12zcab/Handheld-Z80-Retro-Computer/img/PCB.png

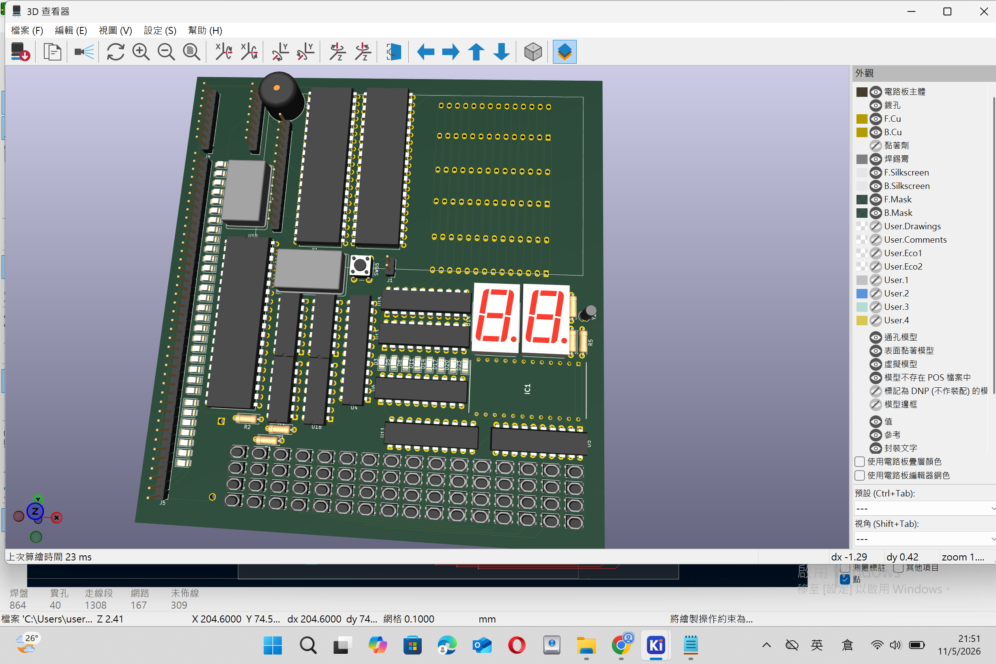
img/PCB.png
