12zcab/Handheld-Z80-Retro-Computer/img/PCBold.png

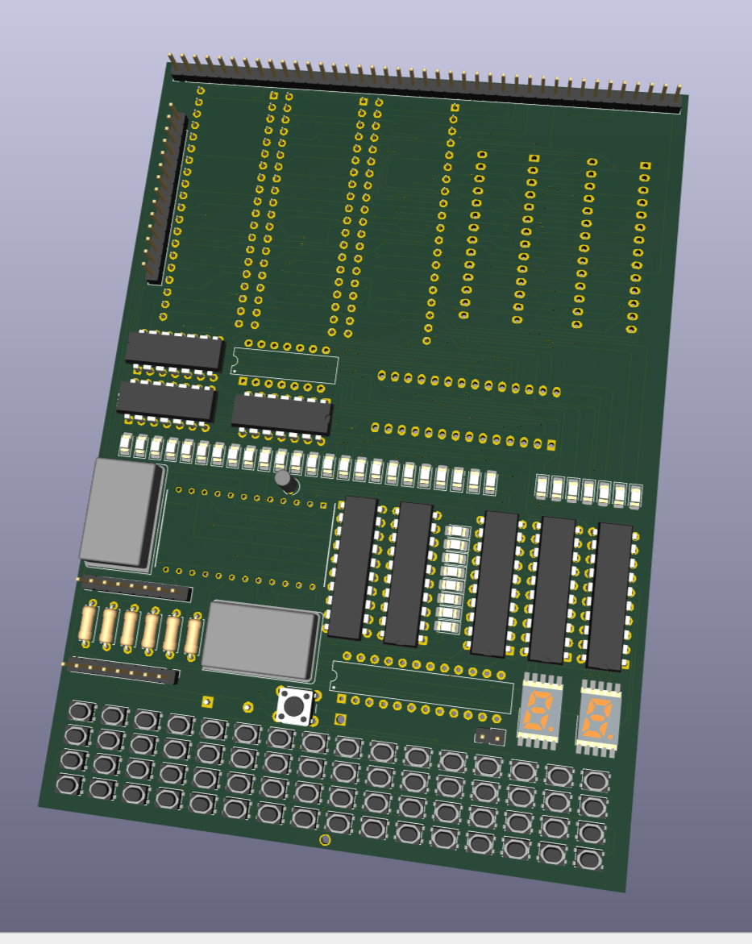
img/PCBold.png
