12zcab/Handheld-Z80-Retro-Computer/img/Route.png

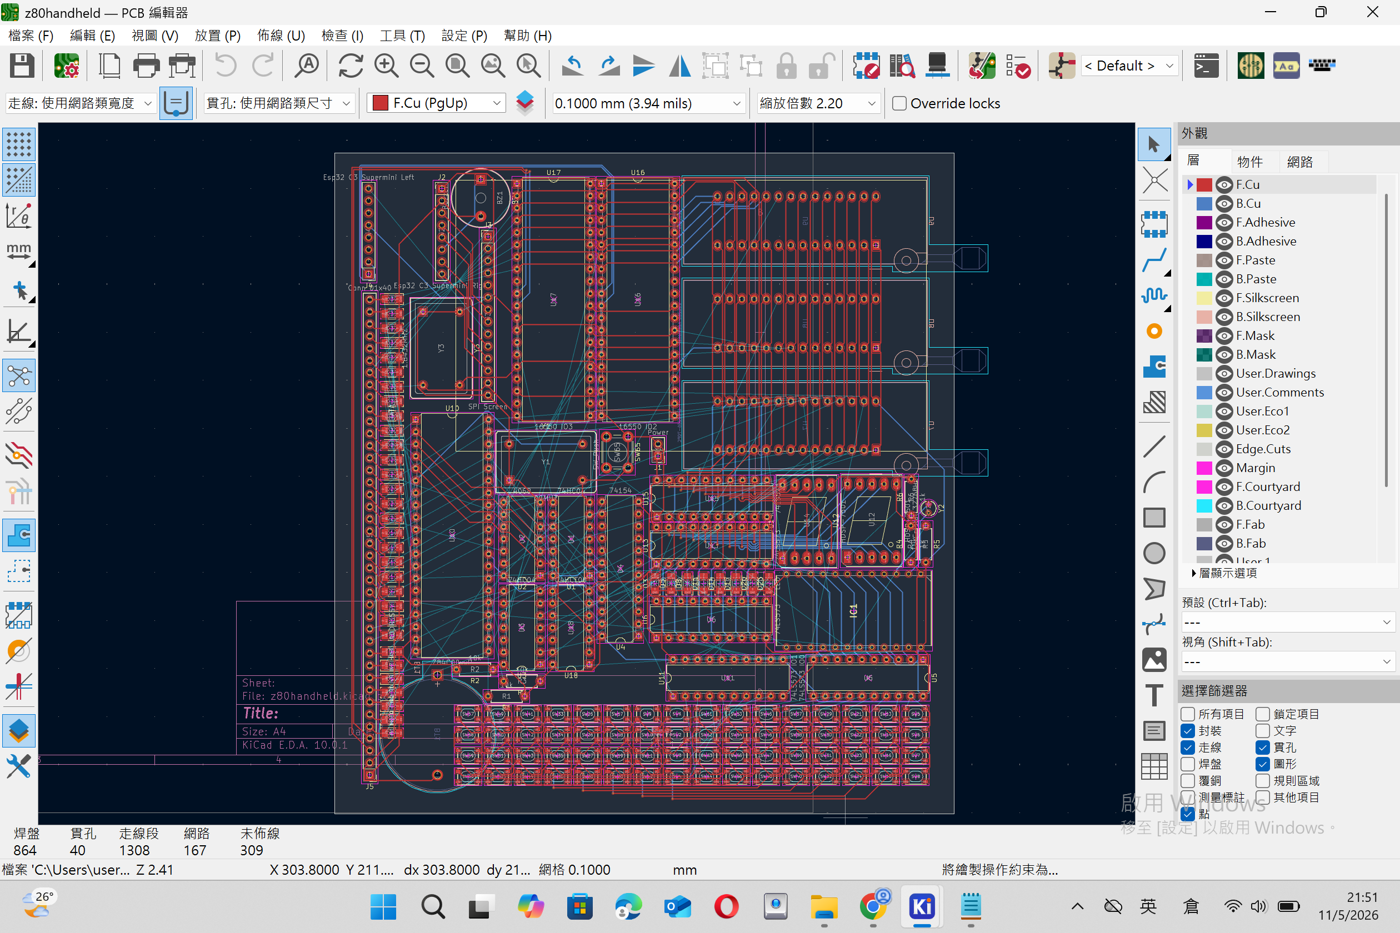
img/Route.png
