12zcab/Handheld-Z80-Retro-Computer/img/Routeold.png

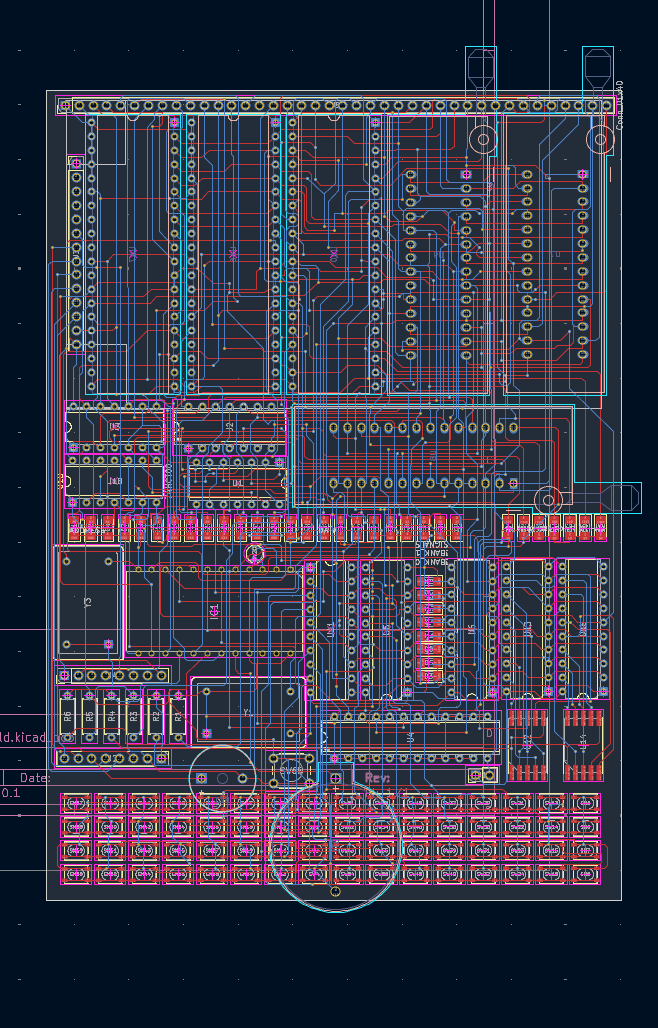
img/Routeold.png
