12zcab/Handheld-Z80-Retro-Computer/ShoppingCartIMG/螢幕擷取畫面 2026-06-13 230417.png

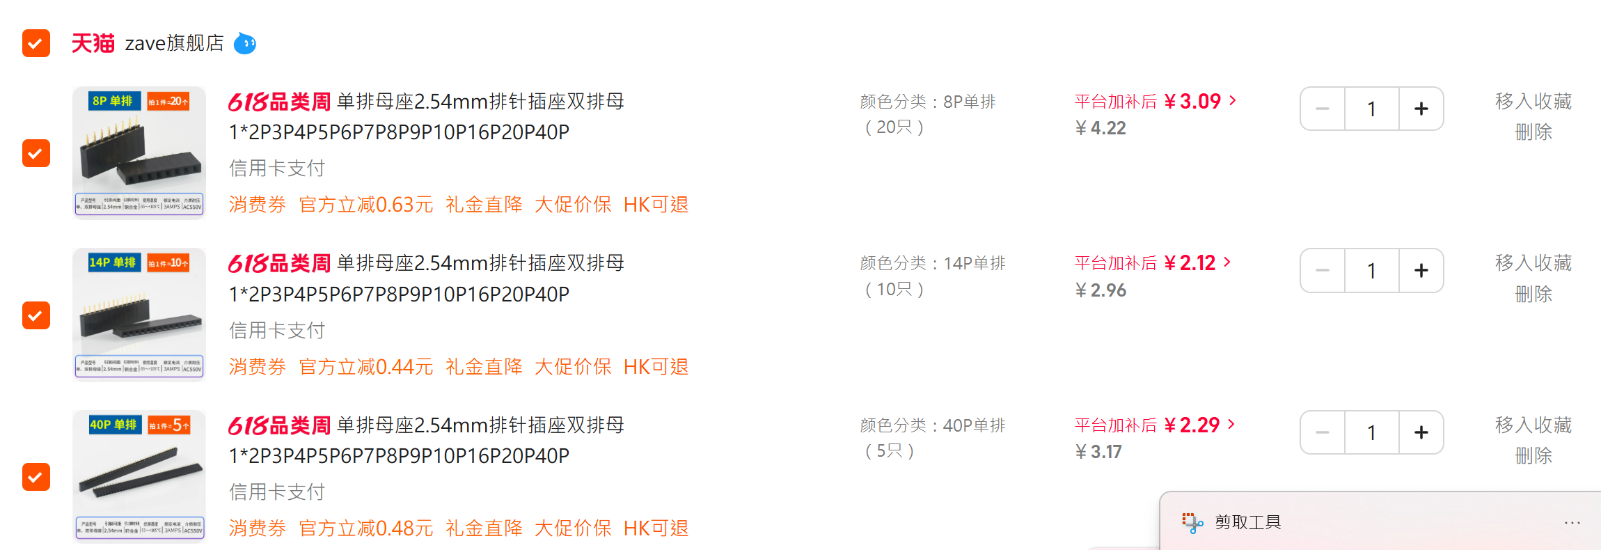
ShoppingCartIMG/螢幕擷取畫面 2026-06-13 230417.png
